vk2diy/23cm/docs/filter-models/clamp-and-attenuator/dual-1n4148-clamp-vs-voltage.png

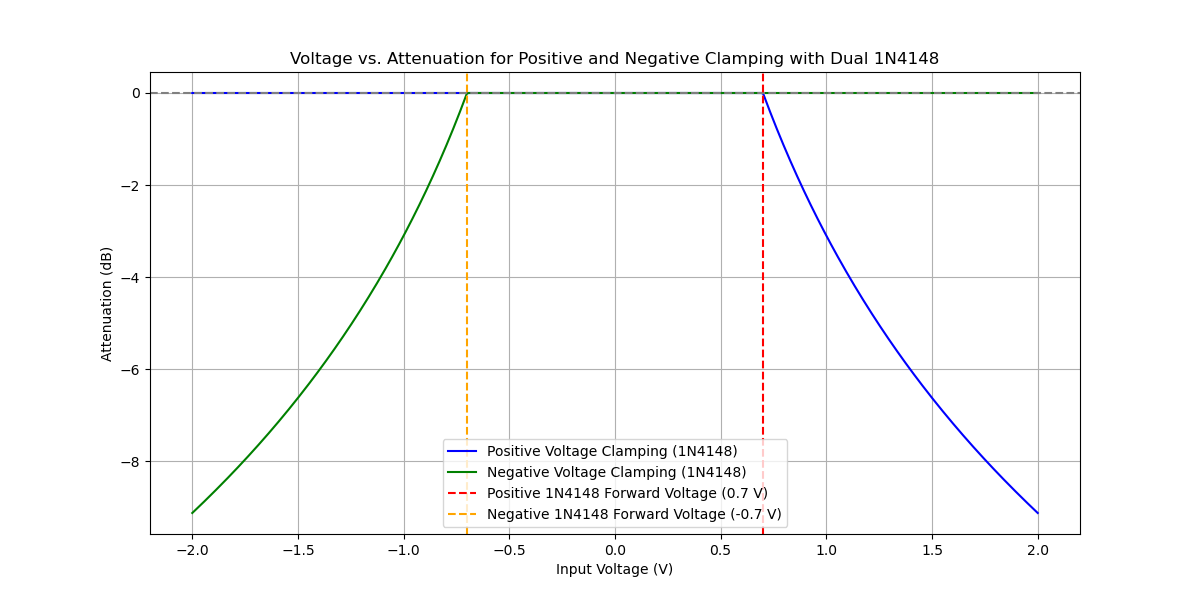
docs/filter-models/clamp-and-attenuator/dual-1n4148-clamp-vs-voltage.png
