vk2diy/23cm/docs/filter-models/ctcss-and-1750mhz-filters/ctcss-and-1750mhz-filters-model.jpg

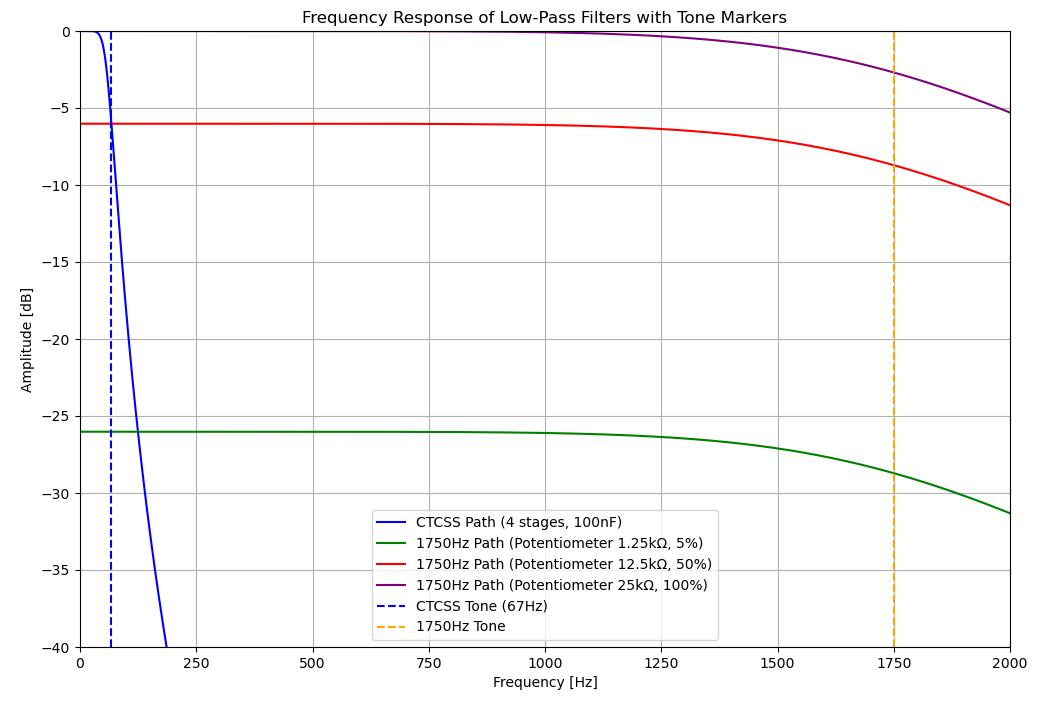
docs/filter-models/ctcss-and-1750mhz-filters/ctcss-and-1750mhz-filters-model.jpg
