vk2diy/23cm/docs/filter-models/fm-audio-high-pass-filter/fm-audio-high-pass-filter-vs-frequency.png

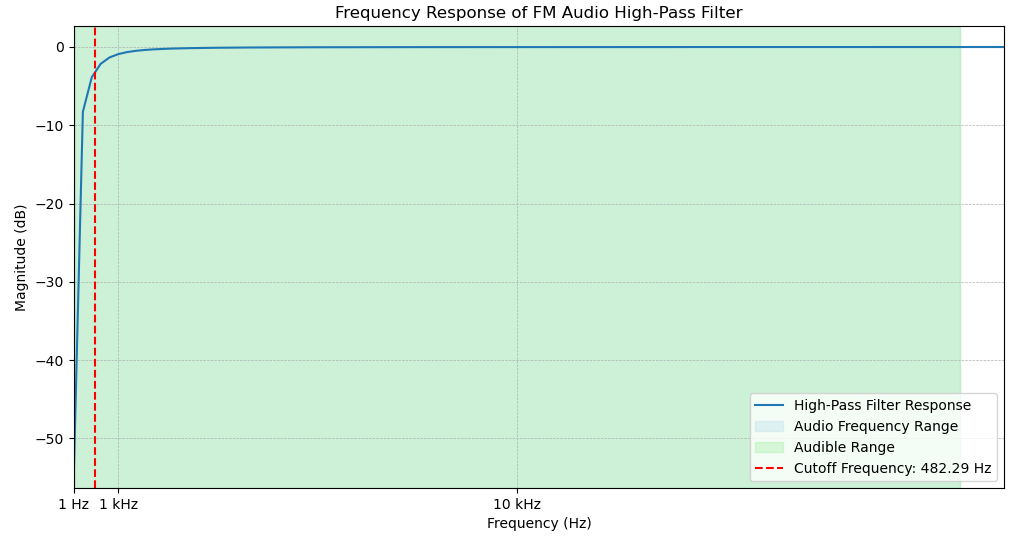
docs/filter-models/fm-audio-high-pass-filter/fm-audio-high-pass-filter-vs-frequency.png
