vk2diy/23cm/docs/filter-models/pa-post-snubber/pa-post-snubber-frequency-vs-attenuation.png

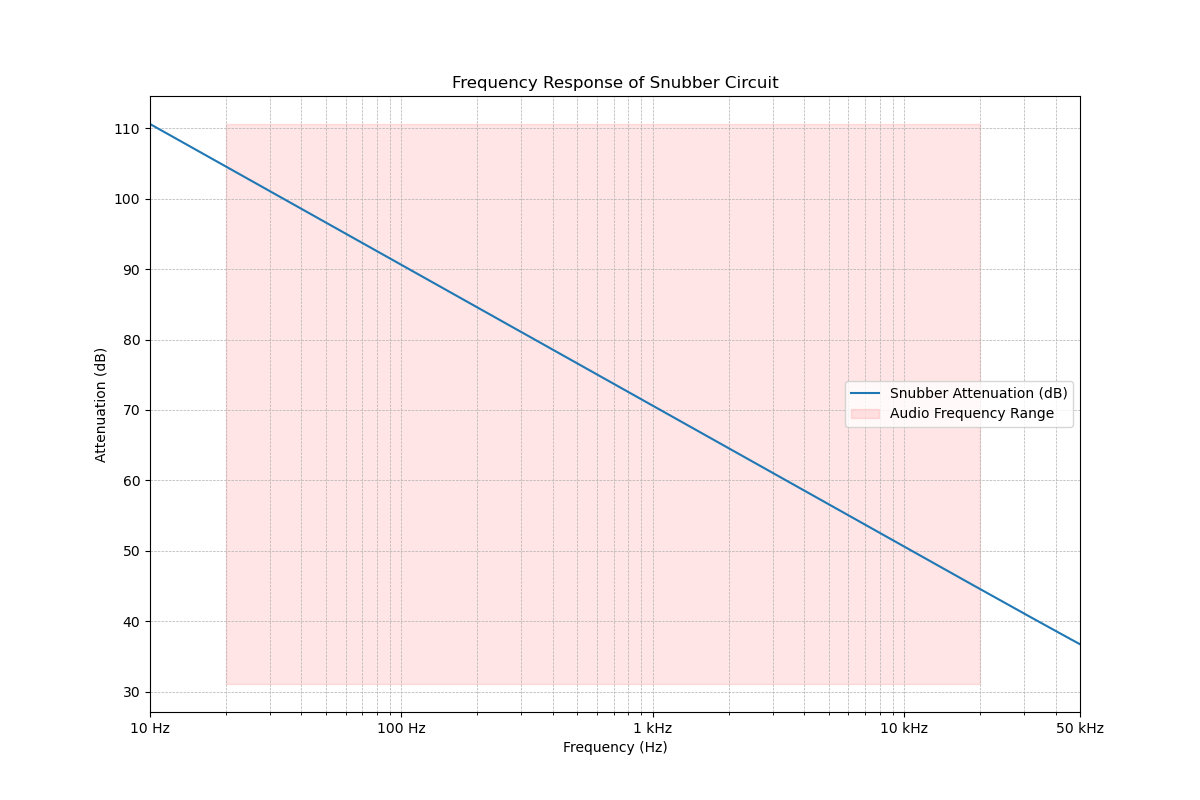
docs/filter-models/pa-post-snubber/pa-post-snubber-frequency-vs-attenuation.png
